dnlbauer/corax-keyboard/docs/images/PXL_20240226_170605892.jpg

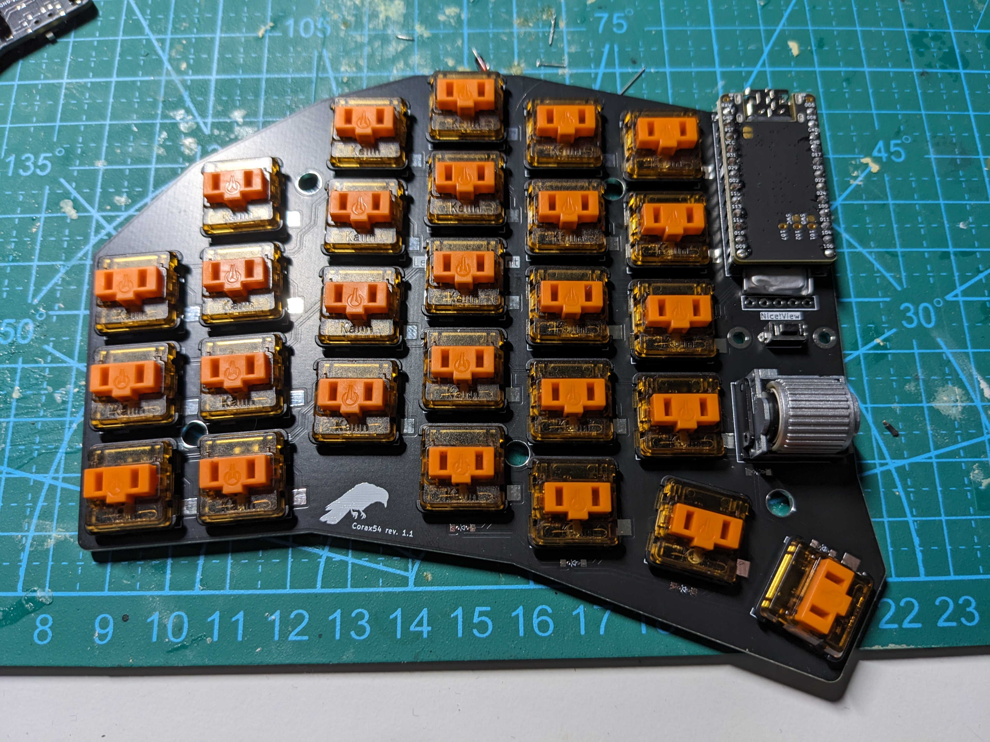
docs/images/PXL_20240226_170605892.jpg
