dnlbauer/corax-keyboard/images/corax54_single.jpg

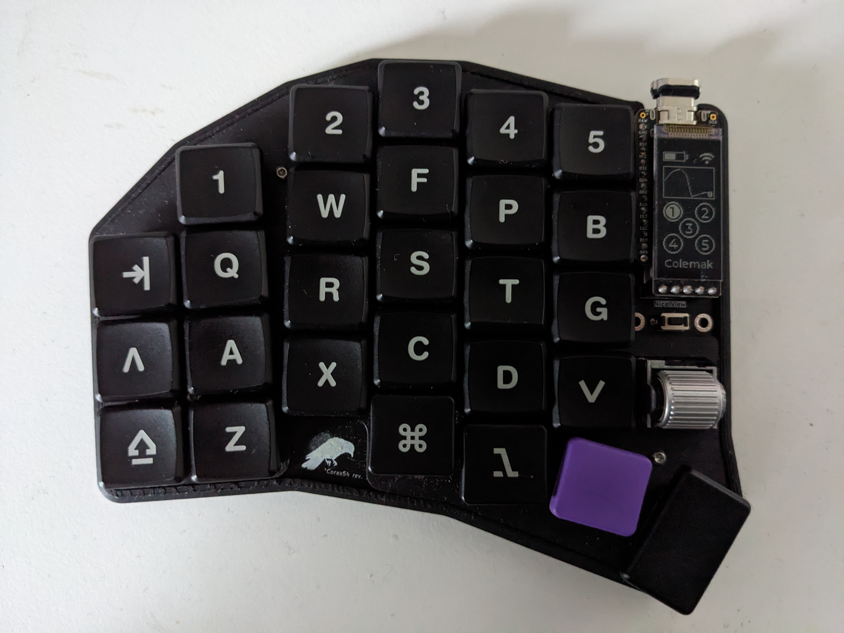
images/corax54_single.jpg
