dnlbauer/corax-keyboard/images/corax56_pcb_render_back.jpg

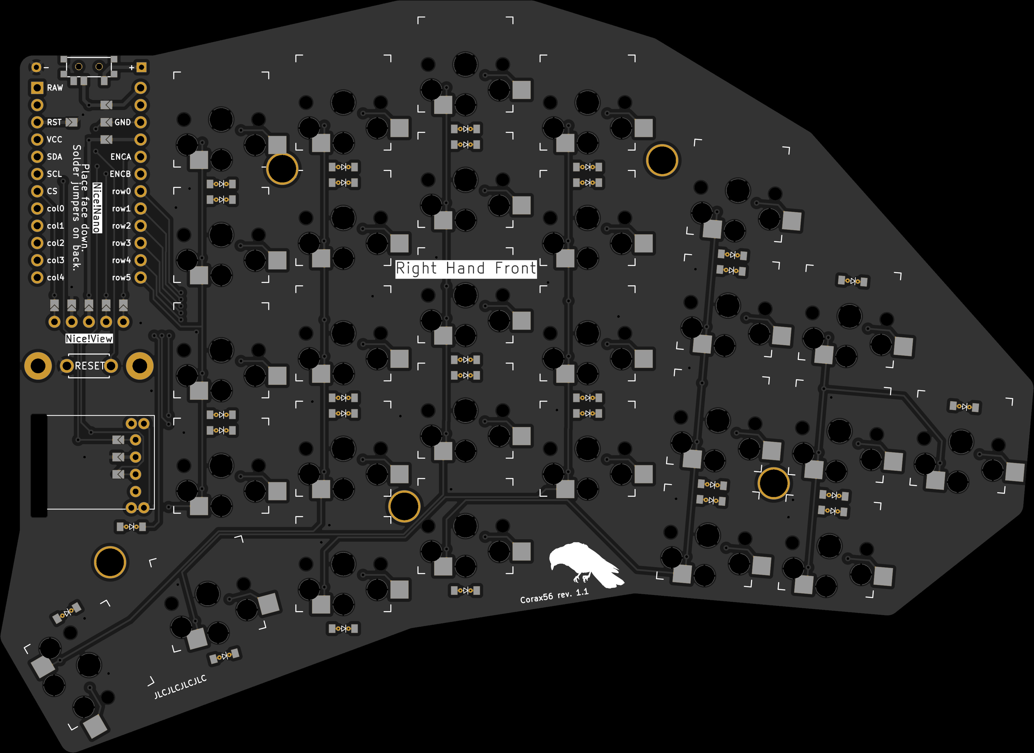
images/corax56_pcb_render_back.jpg
