dnlbauer/corax-keyboard/images/corax56_pcb_render_front.jpg

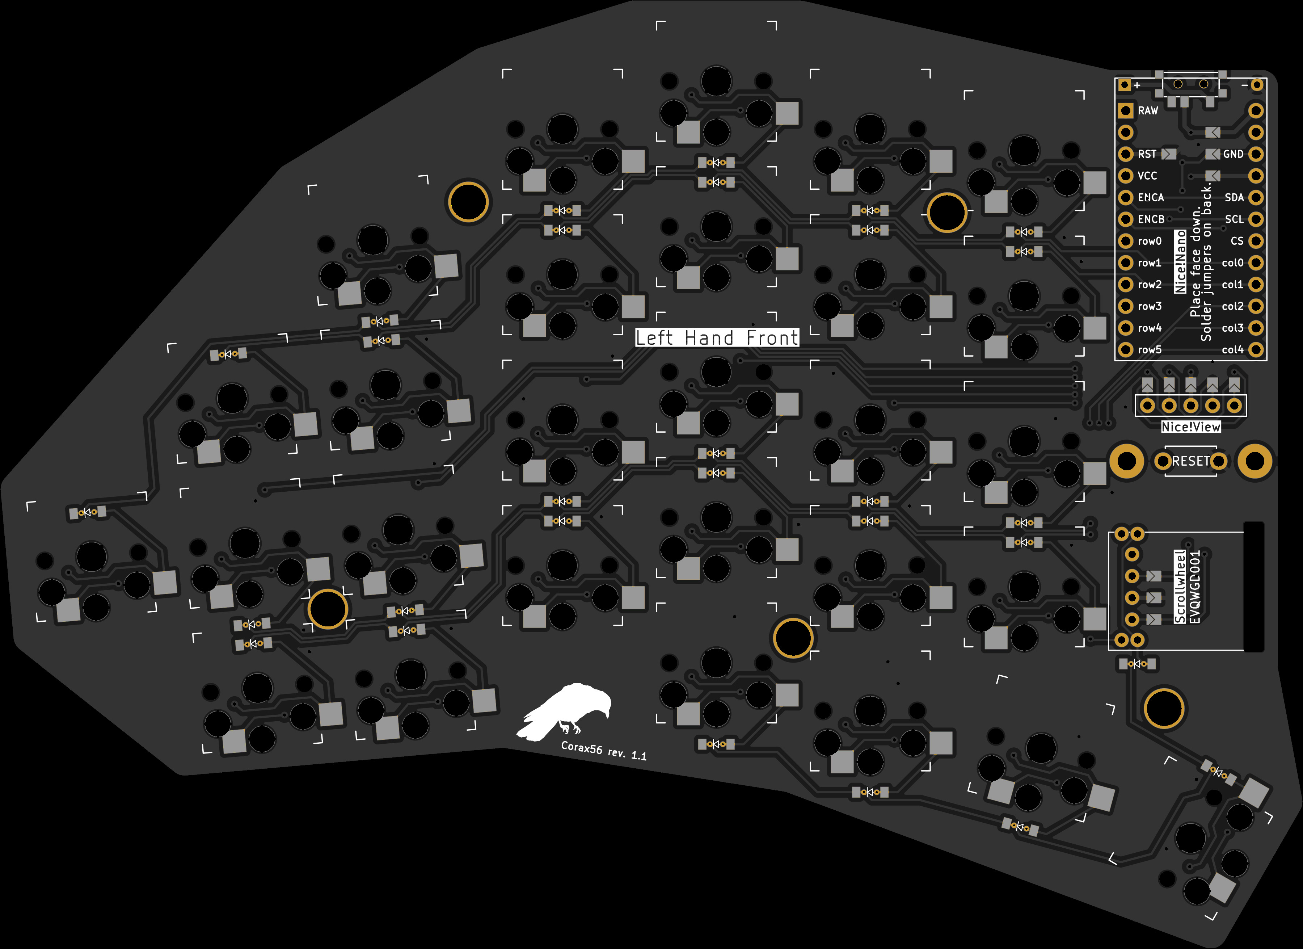
images/corax56_pcb_render_front.jpg
