dnlbauer/corax-keyboard/images/pcb_back.jpg

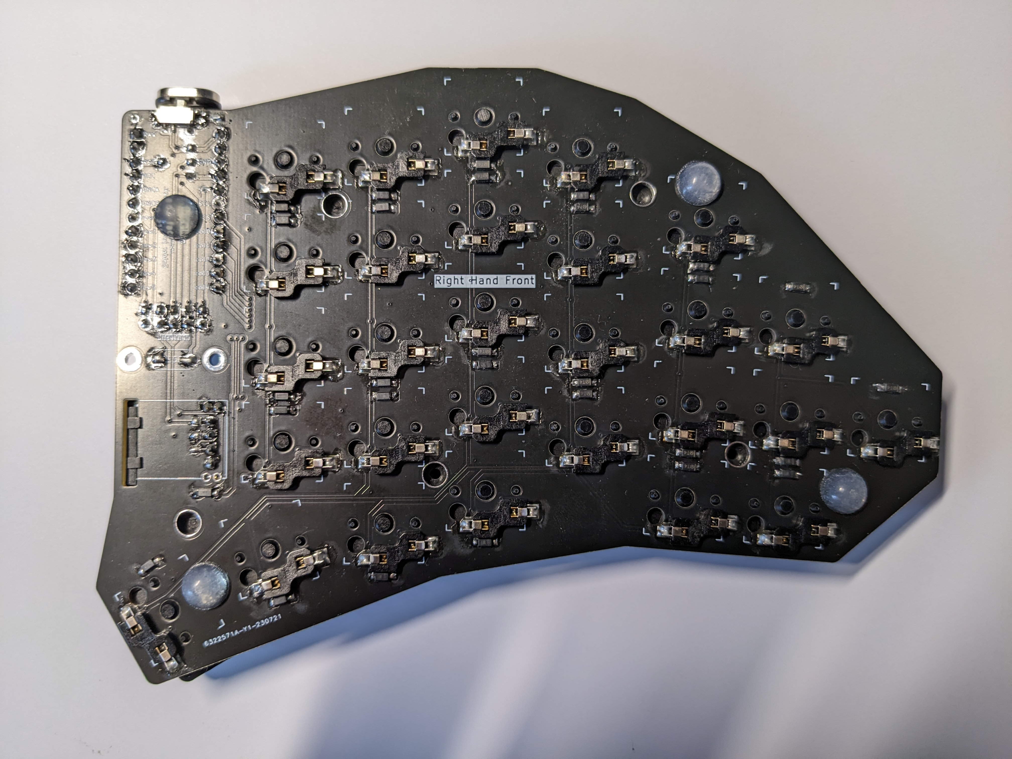
images/pcb_back.jpg
