dnlbauer/corax-keyboard/images/switch.jpg

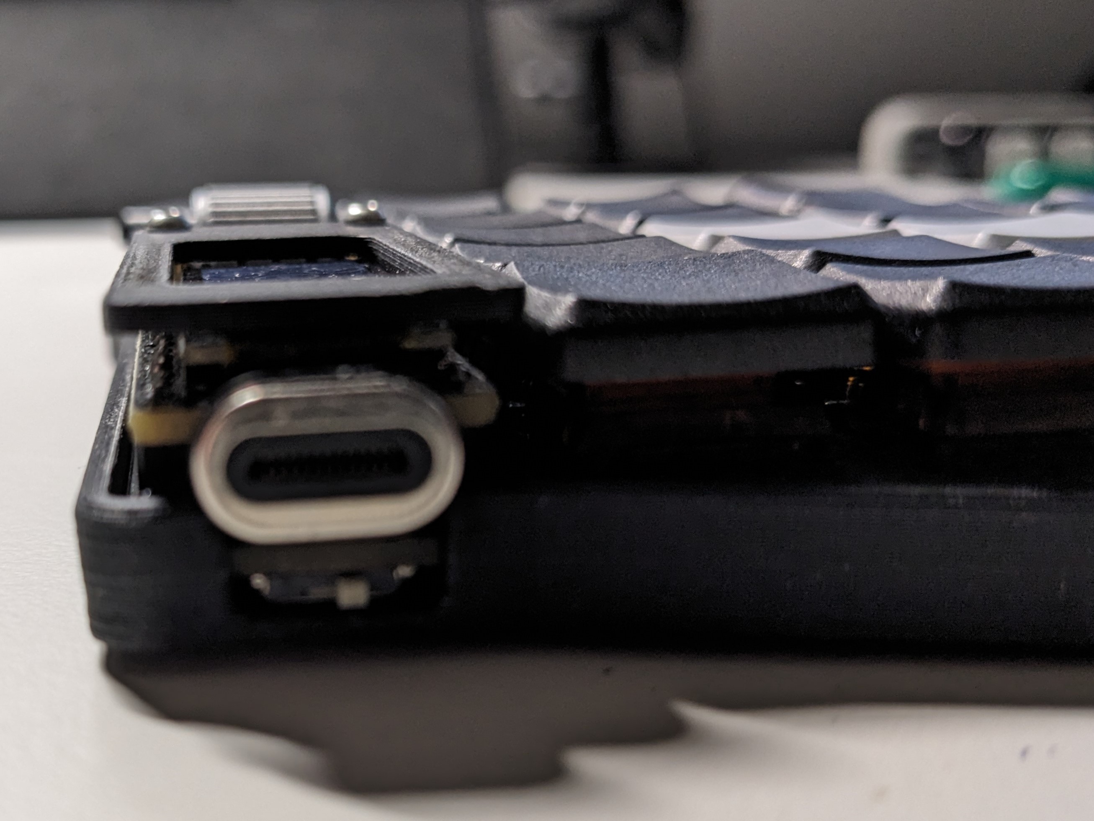
images/switch.jpg
